AndresTejeroMena/DardosLife/image/ajustes.png

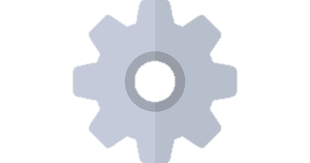
image/ajustes.png
