AndresTejeroMena/DardosLife/image/Conecta4/tablero.png

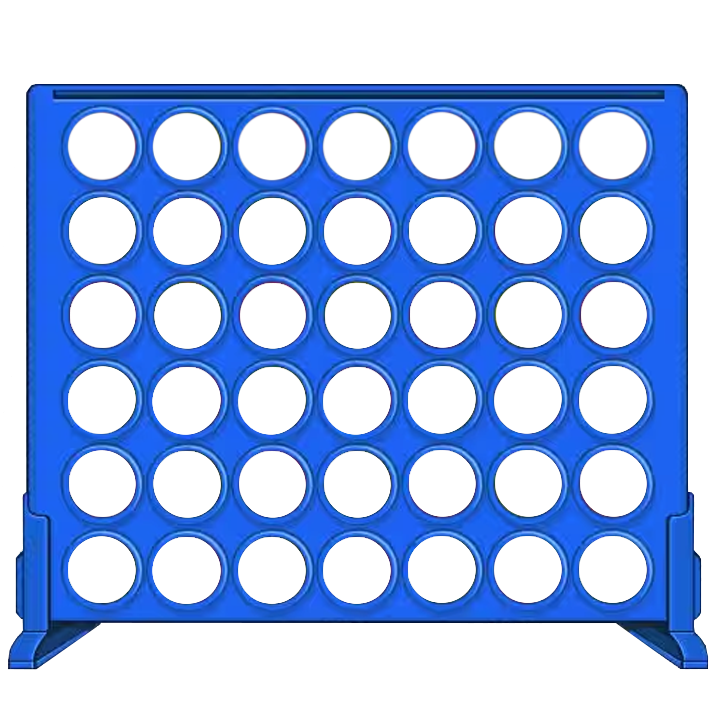
image/Conecta4/tablero.png
