AndresTejeroMena/DardosLife/image/diana.jpg

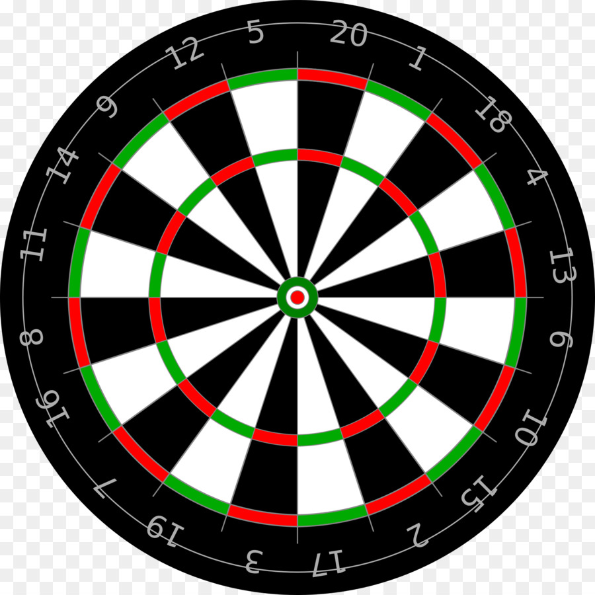
image/diana.jpg
