AndresTejeroMena/DardosLife/image/flecha_menu_sim.png

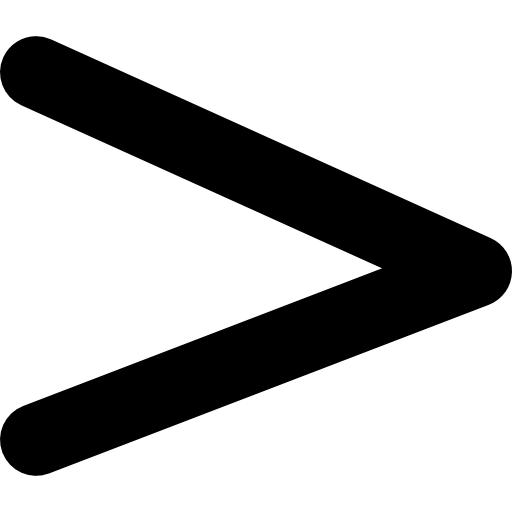
image/flecha_menu_sim.png
