AndresTejeroMena/DardosLife/image/Fondos/cricket_game.png

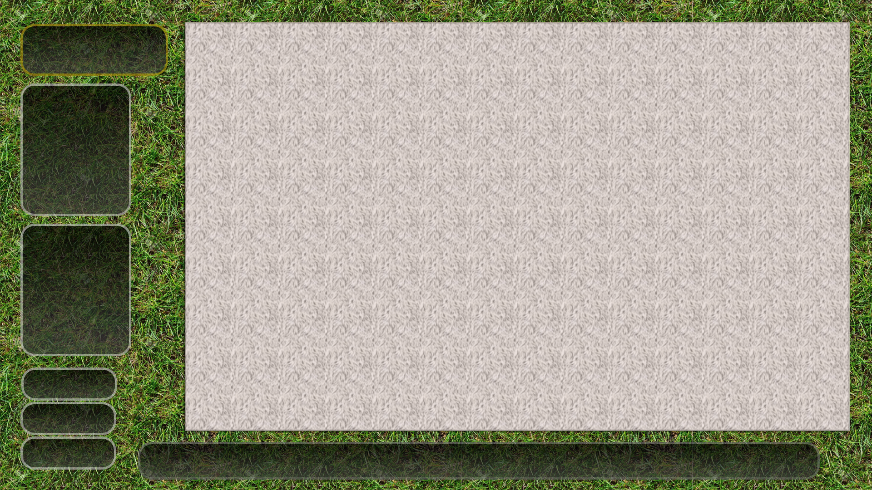
image/Fondos/cricket_game.png
