AndresTejeroMena/DardosLife/image/Fondos/cricket_menu.png

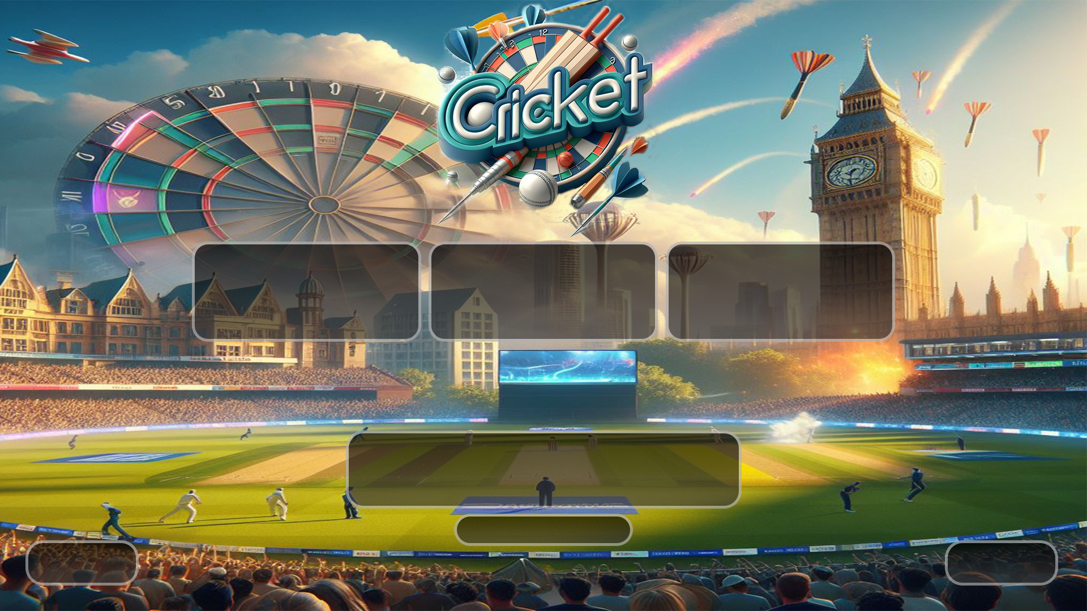
image/Fondos/cricket_menu.png
