AndresTejeroMena/DardosLife/image/Fondos/football_menu.png

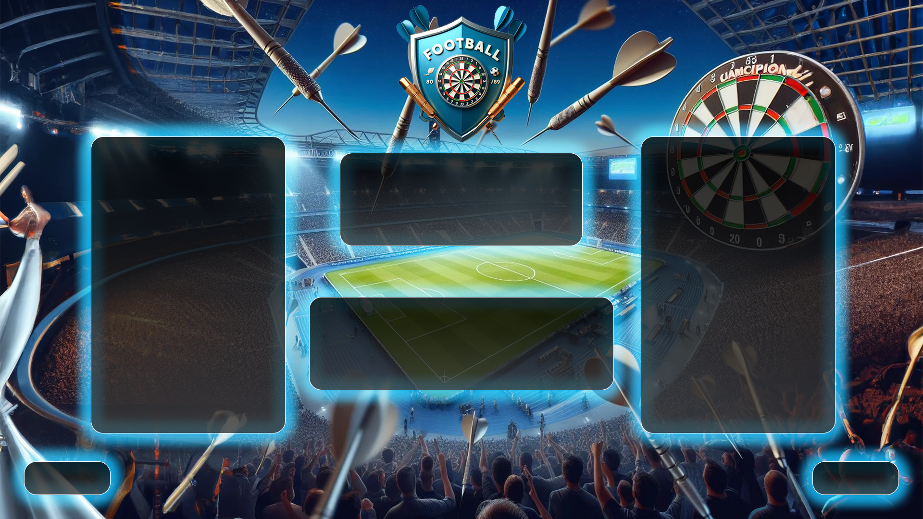
image/Fondos/football_menu.png
