AndresTejeroMena/DardosLife/image/Fondos/hundirlaflota_game.png

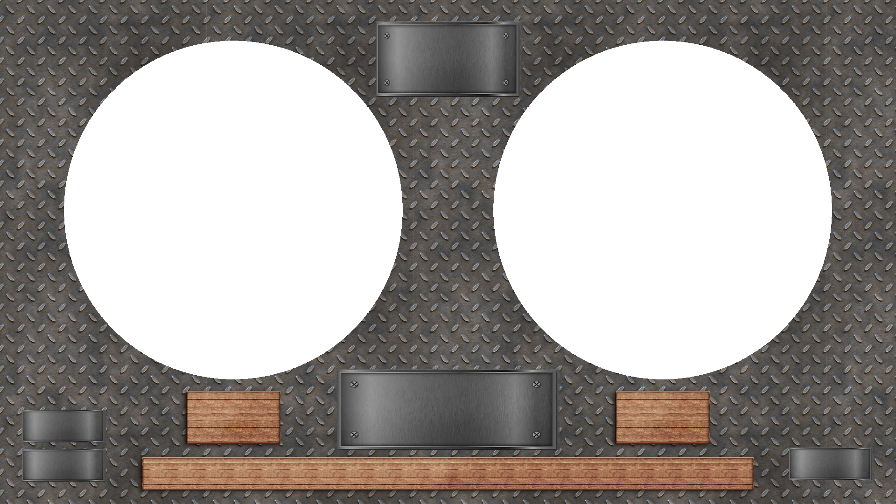
image/Fondos/hundirlaflota_game.png
