AndresTejeroMena/DardosLife/image/Fondos/x01_game.png

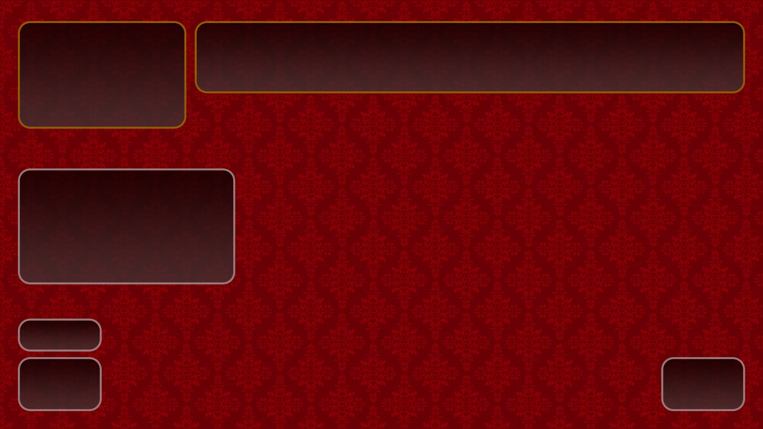
image/Fondos/x01_game.png
