AndresTejeroMena/DardosLife/image/Fondos/x01_menu.png

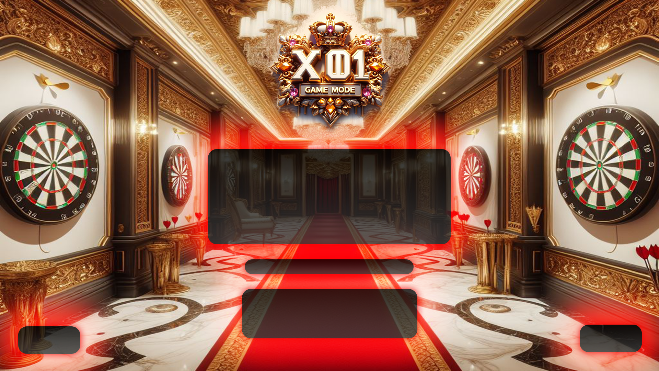
image/Fondos/x01_menu.png
