AndresTejeroMena/DardosLife/image/Fondos/x01_tabla_finales.png

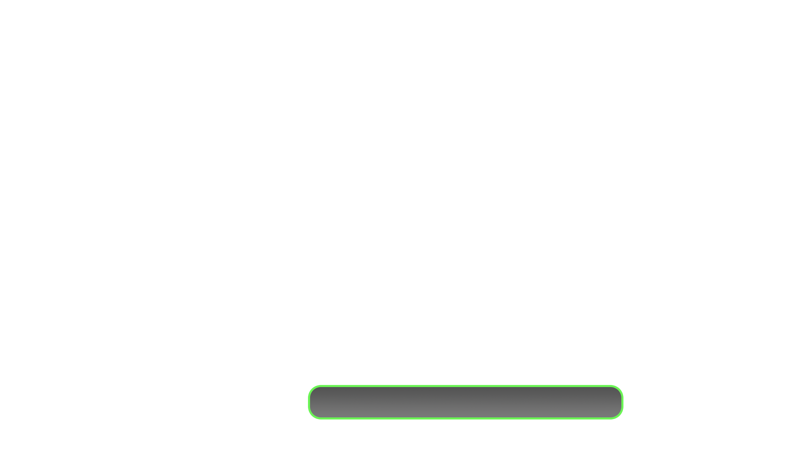
image/Fondos/x01_tabla_finales.png
