AndresTejeroMena/DardosLife/image/Football/dianas.png

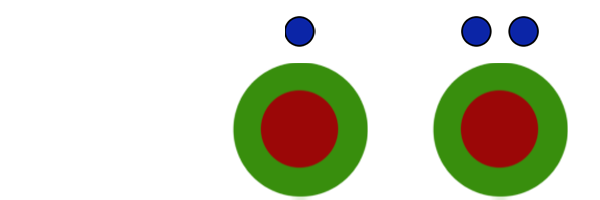
image/Football/dianas.png
