AndresTejeroMena/DardosLife/image/Football/marcas_jugadores.png

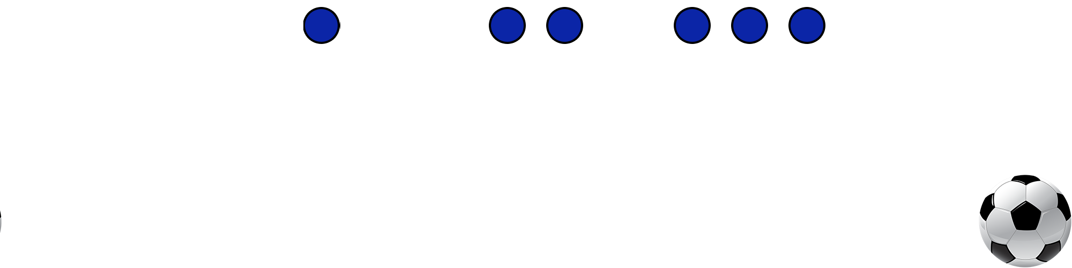
image/Football/marcas_jugadores.png
