AndresTejeroMena/DardosLife/image/HundirLaFlota/acorazado.jpg

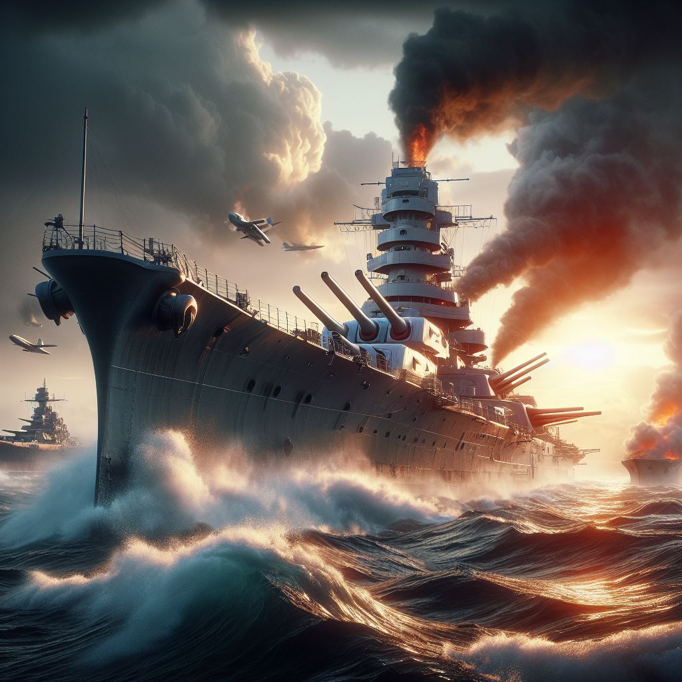
image/HundirLaFlota/acorazado.jpg
