AndresTejeroMena/DardosLife/image/HundirLaFlota/crucero.jpg

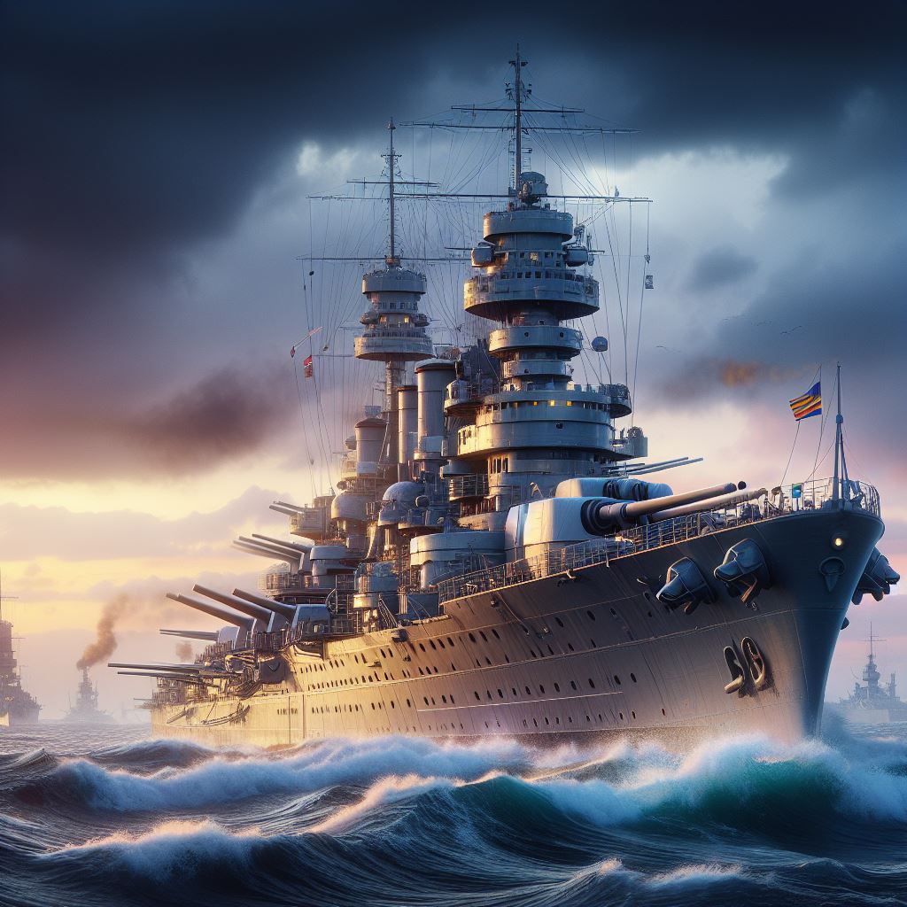
image/HundirLaFlota/crucero.jpg
