AndresTejeroMena/DardosLife/image/HundirLaFlota/radar.jpg

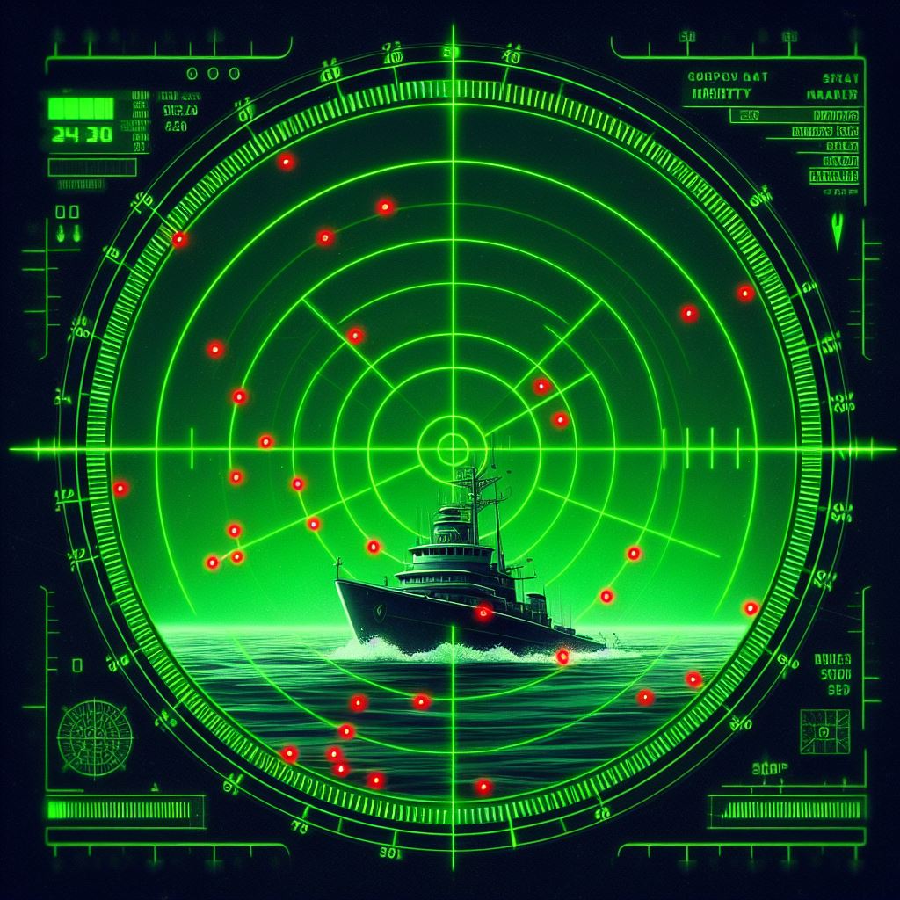
image/HundirLaFlota/radar.jpg
