AndresTejeroMena/DardosLife/image/HundirLaFlota/submarino.jpg

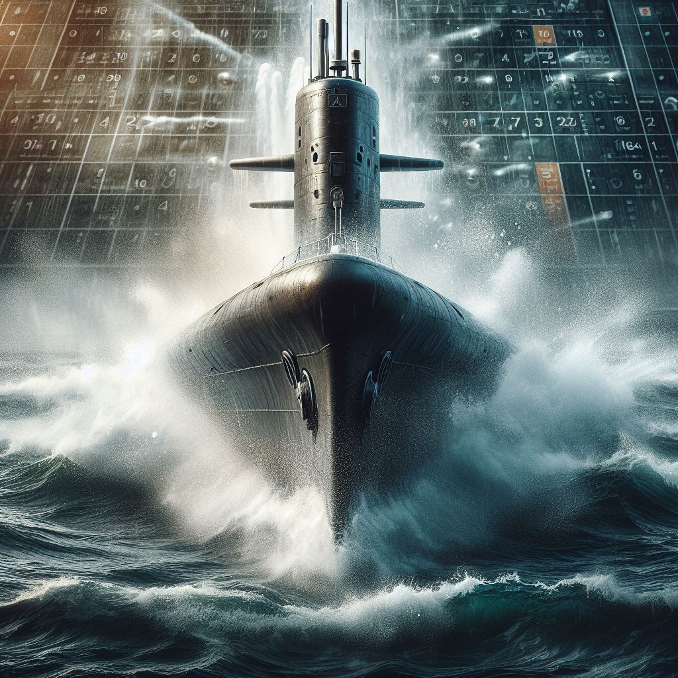
image/HundirLaFlota/submarino.jpg
