AndresTejeroMena/DardosLife/image/ModosDeJuego/Connect4.jpg

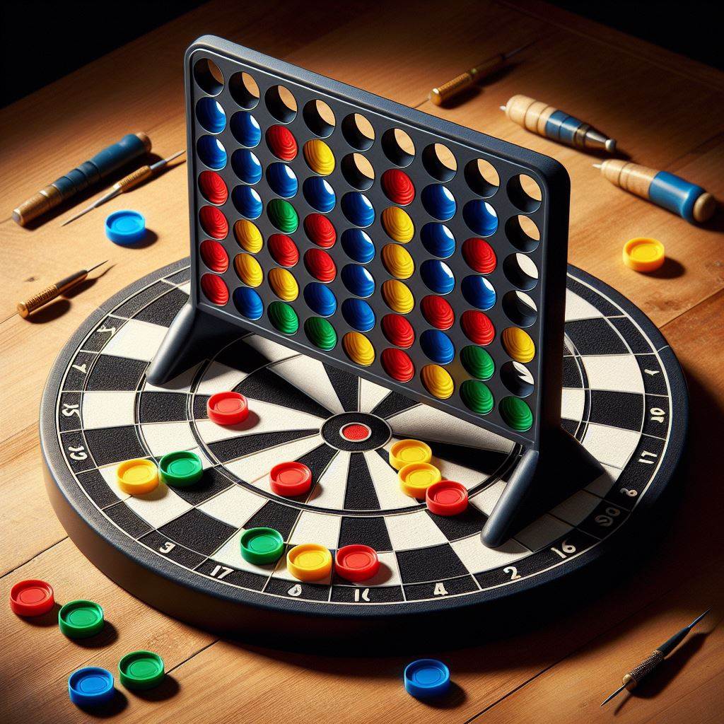
image/ModosDeJuego/Connect4.jpg
