AndresTejeroMena/DardosLife/image/ModosDeJuego/Cricket.jpg

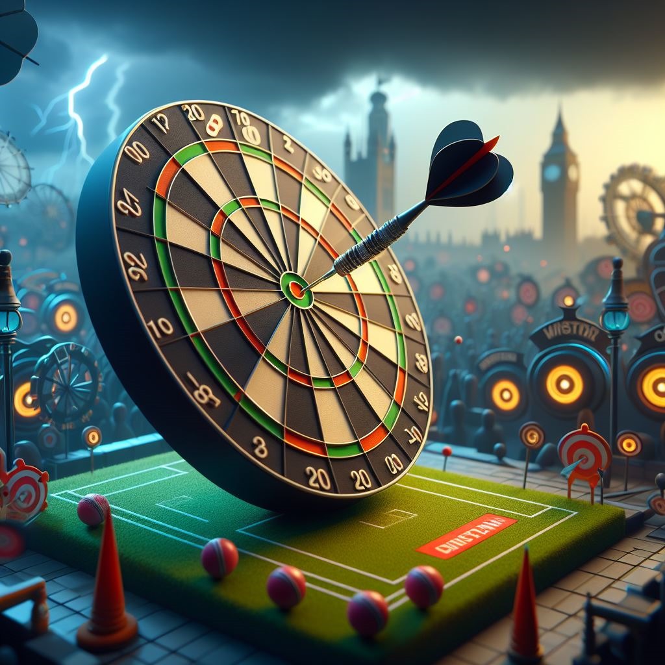
image/ModosDeJuego/Cricket.jpg
