AndresTejeroMena/DardosLife/image/ModosDeJuego/Football.jpg

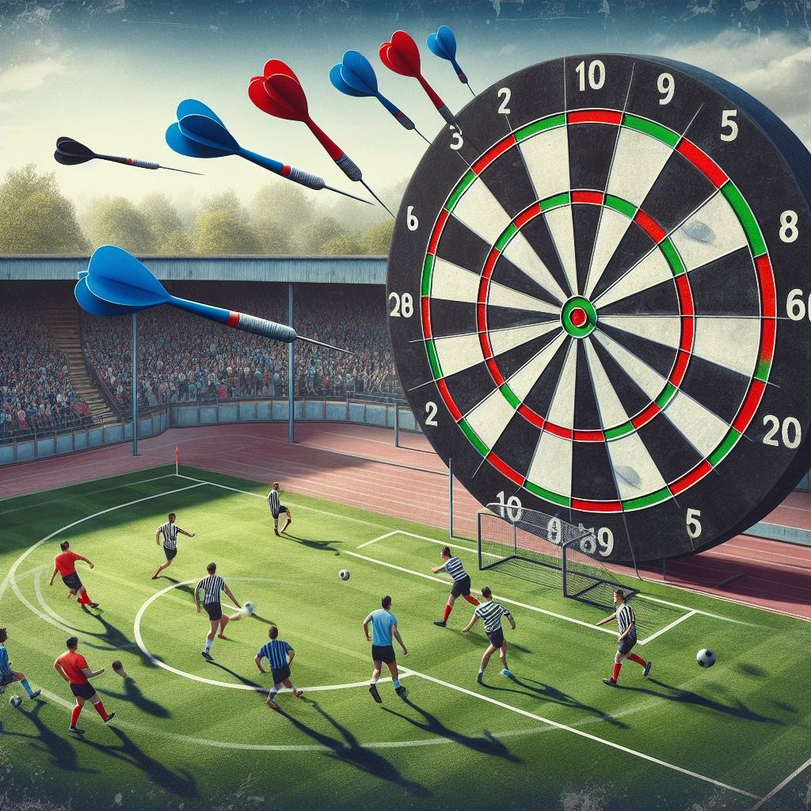
image/ModosDeJuego/Football.jpg
