AndresTejeroMena/DardosLife/image/ModosDeJuego/HundirLaFlota.jpg

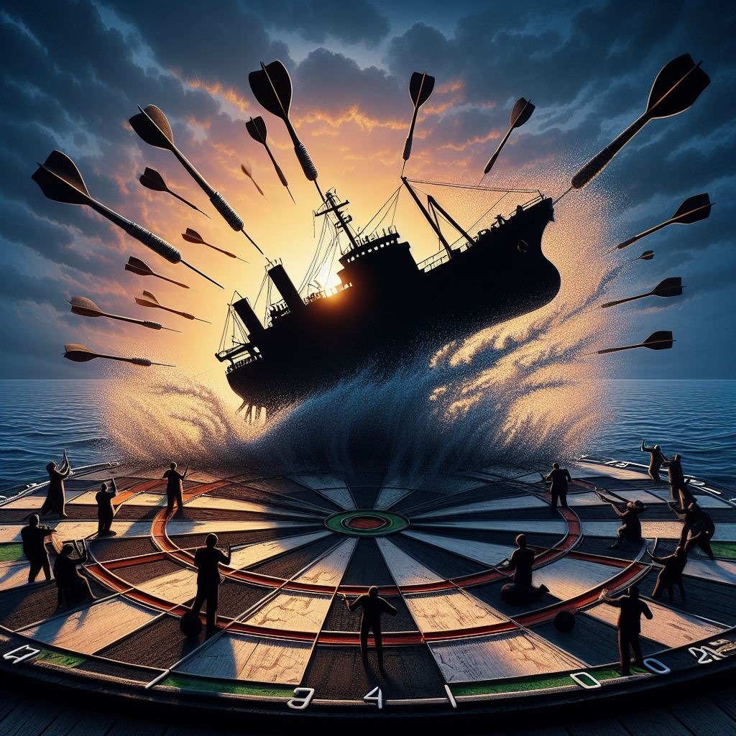
image/ModosDeJuego/HundirLaFlota.jpg
